seb201/tideanzeiger/Code/Numbers.h

const unsigned char CH[] PROGMEM = {

  //Arabisch
  3, 8, B00000000, B00000000, B00000000, B00000000, B00000000, // space
  1, 8, B01011111, B00000000, B00000000, B00000000, B00000000, // !
  3, 8, B00000011, B00000000, B00000011, B00000000, B00000000, // "
  5, 8, B00010100, B00111110, B00010100, B00111110, B00010100, // #
  4, 8, B00100100, B01101010, B00101011, B00010010, B00000000, // $
  5, 8, B01100011, B00010011, B00001000, B01100100, B01100011, // %
  5, 8, B00110110, B01001001, B01010110, B00100000, B01010000, // &
  1, 8, B00000011, B00000000, B00000000, B00000000, B00000000, // '
  3, 8, B00011100, B00100010, B01000001, B00000000, B00000000, // (
  3, 8, B01000001, B00100010, B00011100, B00000000, B00000000, // )
  5, 8, B00101000, B00011000, B00001110, B00011000, B00101000, // *
  5, 8, B00001000, B00001000, B00111110, B00001000, B00001000, // +
  2, 8, B10110000, B01110000, B00000000, B00000000, B00000000, // ,
  4, 8, B00001000, B00001000, B00001000, B00001000, B00000000, // -
  2, 8, B01100000, B01100000, B00000000, B00000000, B00000000, // .
  4, 8, B01100000, B00011000, B00000110, B00000001, B00000000, // /
  4, 8, B00111110, B01000001, B01000001, B00111110, B00000000, // 0
  3, 8, B01000010, B01111111, B01000000, B00000000, B00000000, // 1
  5, 8, B01100010, B01010001, B01001001, B01000110, B00000000, // 2
  5, 8, B00100010, B01000001, B01001001, B00110110, B00000000, // 3
  4, 8, B00011000, B00010100, B00010010, B01111111, B00000000, // 4
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
  3, 8, B00001000, B00110110, B01000001, B00000000, B00000000, // {
  1, 8, B01111111, B00000000, B00000000, B00000000, B00000000, // |
  3, 8, B01000001, B00110110, B00001000, B00000000, B00000000, // }
  4, 8, B00001000, B00000100, B00001000, B00000100, B00000000, // ~
};
